Pegoku/Monopoly-Electronic-V2/CODE/esp32Code/include/display_ui.h

#pragma once

#include <Adafruit_GFX.h>
#include <Adafruit_ST7789.h>

#include "config.h"
#include "game_logic.h"

class DisplayUi {
 public:
  bool begin();
  void render(const GameLogic &game, float batteryPercent);
  void renderProgramming(const char *category, uint8_t itemId, const char *detail, bool armWrite, const char *message);
  void renderLobby(uint8_t registeredCount, uint8_t requiredCount, const bool activePlayers[GAME_MAX_PLAYERS], bool fundingStage, const char *message);
  void renderActionMenu(uint8_t selected);

 private:
  void drawHome(const GameLogic &game);
  void drawWaitCard(const ActionContext &ctx, bool fullRedraw = true);
  void drawPropertyUnowned(const GameLogic &game, const ActionContext &ctx);
  void drawPropertyOwned(const GameLogic &game, const ActionContext &ctx);
  void drawEvent(const ActionContext &ctx);
  void drawAuction(const ActionContext &ctx);
  void drawDebt(const ActionContext &ctx);
  void drawGo();
  void drawTrain();
  void drawJail();
  void drawWinner(const GameLogic &game, const ActionContext &ctx);
  void drawStatusBar(UiState state, float batteryPercent);
  void clearMain();

  Adafruit_ST7789 tft_{&SPI, PIN_TFT_CS, PIN_TFT_DC, PIN_TFT_RST};
  bool hasLastState_ = false;
  UiState lastState_ = UiState::HOME;
  int lastBattery_ = -1;
};
